humancomputerintegration/trigeminal-based-temperature-illusions/Schematic/Kicad/TrigTempIll_schematic.kicad_pcb

## EAGLE design schema/mjBeep/alimentazione.sch

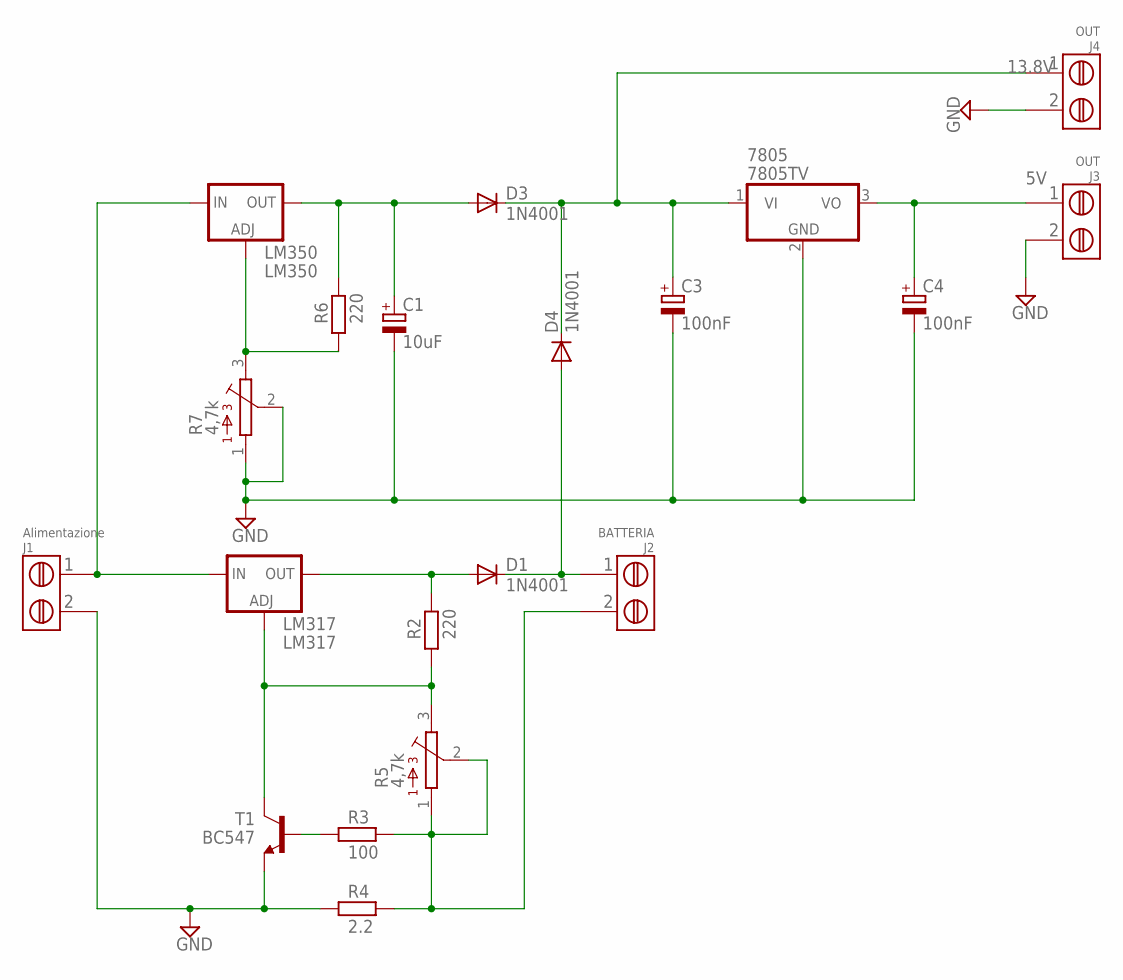
[picture p8: schematic alimentazione.sch]

Parts:
7805: 7805TV; TO220V
C1: 10uF; E2,5-6
C3, C4: 100nF; E2,5-6
D1, D3, D4: 1N4001; DO41-10
J1: Alimentazione; MORSETTIERA
J2: BATTERIA; MORSETTIERA
J3, J4: OUT; MORSETTIERA
LM317: LM317; 317TS
LM350: LM350; 317TS
R2, R6: 220; R1/4W
R3: 100; R1/4W
R4: 2.2; R1/4W
R5, R7: 4,7k; CA9V
T1: BC547; TO92

Connections:
5V: 7805.3 (VO), C4.+, J3.1
13.8V: 7805.1 (VI), C3.+, D3.C (K), D4.C (K), J4.1
+BAT: D1.C (K), D4.A, J2.1
-BAT: J2.2, R3.2, R4.2, R5.1, R5.2
GND: 7805.2 (GND), C1.-, C3.-, C4.-, J1.2, J3.2, J4.2, R4.1, R7.1, R7.2, T1.1 (E)
unnamed: C1.+, D3.A, LM350.2 (OUT), R6.2
unnamed: R3.1, T1.2 (B)
unnamed: LM350.1 (ADJ), R6.1, R7.3
unnamed: J1.1, LM317.3 (IN), LM350.3 (IN)
unnamed: D1.A, LM317.2 (OUT), R2.2
unnamed: LM317.1 (ADJ), R2.1, R5.3, T1.3 (C)
