humancomputerintegration/trigeminal-based-temperature-illusions/Schematic/Kicad/TrigTempIll_schematic.kicad_pcb

## EAGLE design schema/mjBeep/boardBase3.sch

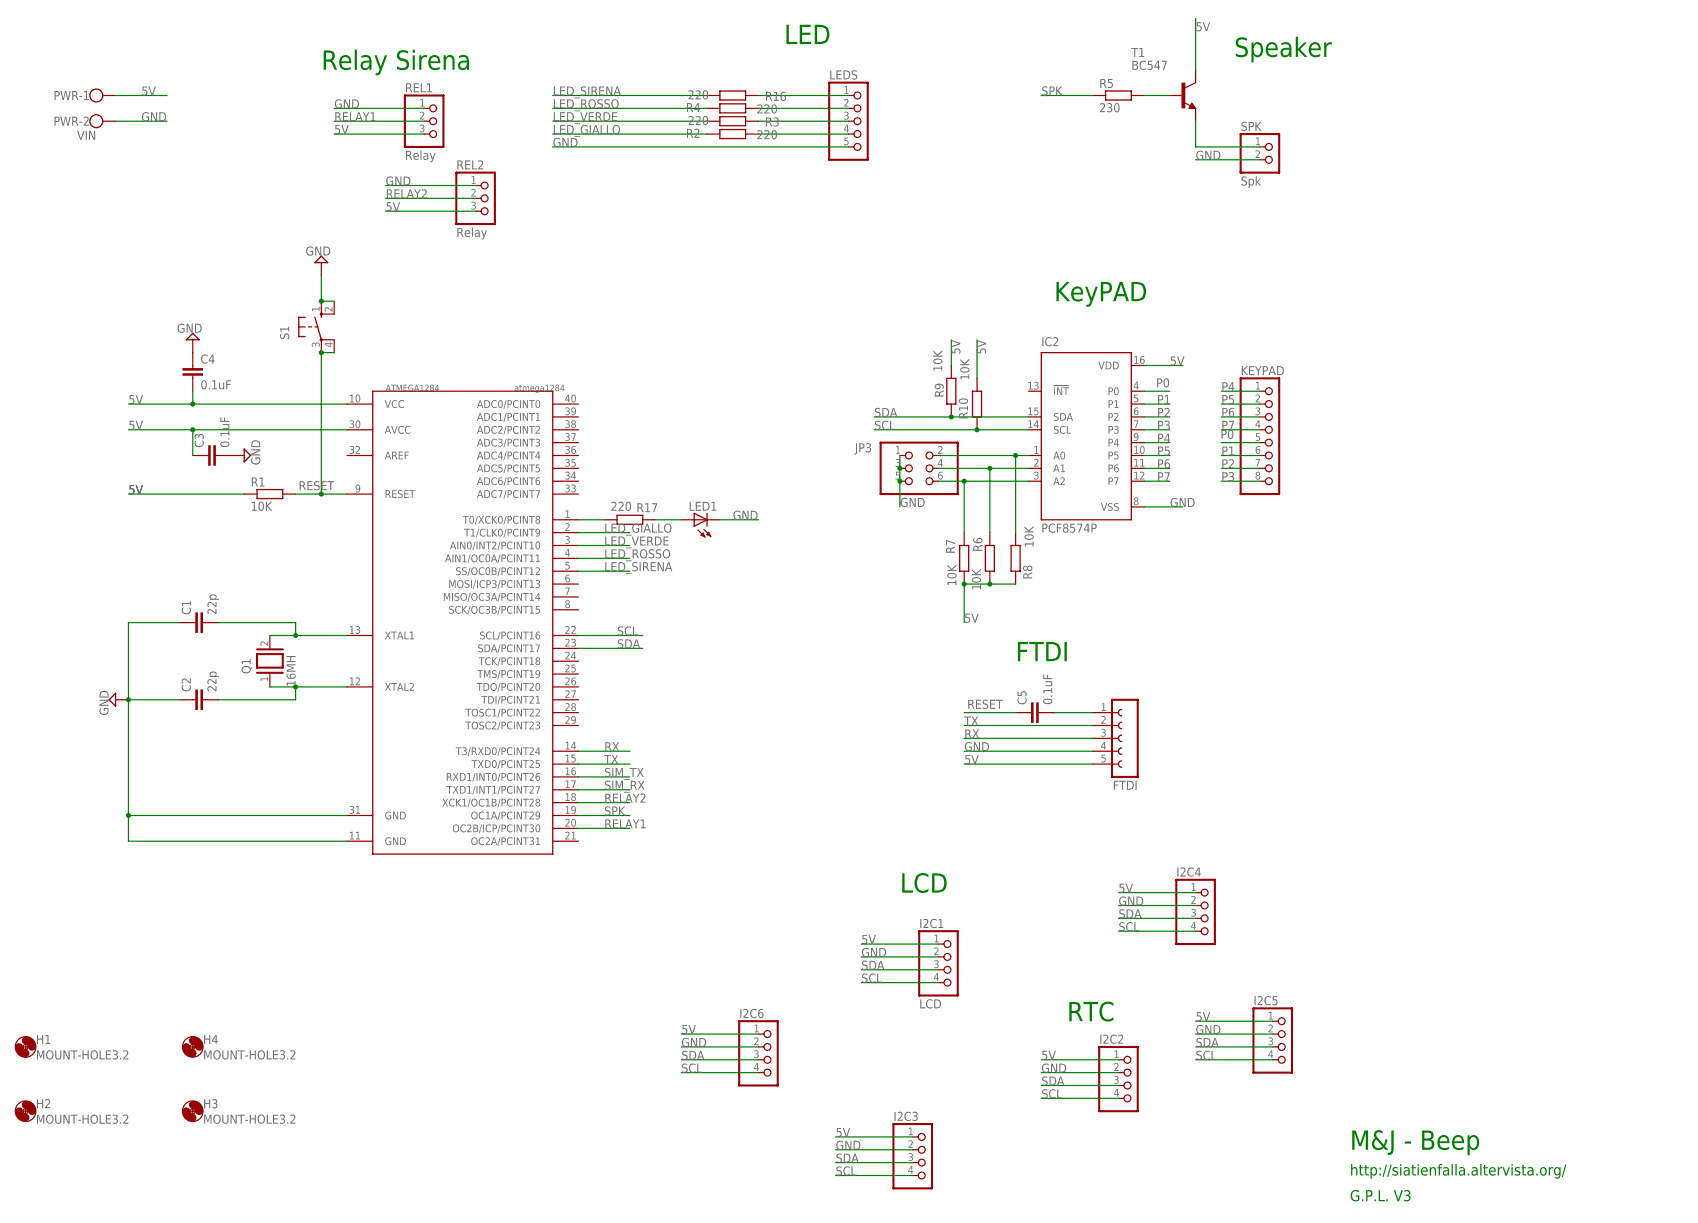
[picture p10: schematic boardBase3.sch]

Parts:
ATMEGA1284: atmega1284; DIL40
C1, C2: 22p; C025-024X044
C3, C4, C5: 0.1uF; C025-025X050
FTDI: FE05-1
H1, H2, H3, H4: MOUNT-HOLE3.2; 3,2
I2C1: LCD; 1X04
I2C2, I2C3, I2C4, I2C5, I2C6: PINHD-1X4; 1X04
IC2: PCF8574P; DIL16
JP3: PINHD-2X3; 2X03
KEYPAD: PINHD-1X8; 1X08
LED1: LED3MM
LEDS: PINHD-1X5; 1X05
PWR: VIN; W237-102
Q1: 16MH; QS
R1: 10K; 0207/10
R2, R3, R4, R16, R17: 220; 0207/2V
R5: 230; 0207/2V
R6, R7, R8, R9, R10: 10K; 0207/2V
REL1, REL2: Relay; 1X03
S1: 10-XX; B3F-10XX
SPK: Spk; 1X02
T1: BC547; TO92

Connections:
5V: ATMEGA1284.10 (VCC), ATMEGA1284.30 (AVCC), C3.1, C4.2, FTDI.5, I2C1.1, I2C2.1, I2C3.1, I2C4.1, I2C5.1, I2C6.1, IC2.16 (VDD), PWR.1, R1.1, R6.1, R7.2, R8.2, R9.2, R10.1, REL1.3, REL2.3, T1.3 (C)
GND: ATMEGA1284.11 (GND), ATMEGA1284.31 (GND), C1.1, C2.1, C3.2, C4.1, FTDI.4, I2C1.2, I2C2.2, I2C3.2, I2C4.2, I2C5.2, I2C6.2, IC2.8 (VSS), JP3.1, JP3.3, JP3.5, LED1.K (C), LEDS.5, PWR.2, REL1.1, REL2.1, S1.1 (S), S1.2 (S1), SPK.2
LED_GIALLO: ATMEGA1284.2 (T1/CLK0/PCINT9), R2.2
LED_ROSSO: ATMEGA1284.4 (AIN1/OC0A/PCINT11), R4.2
LED_SIRENA: ATMEGA1284.5 (SS/OC0B/PCINT12), R16.1
LED_VERDE: ATMEGA1284.3 (AIN0/INT2/PCINT10), R3.1
unnamed: ATMEGA1284.12 (XTAL2), C2.2, Q1.1
unnamed: ATMEGA1284.13 (XTAL1), C1.2, Q1.2
unnamed: IC2.1 (A0), JP3.2, R8.1
unnamed: C5.2, FTDI.1
unnamed: IC2.2 (A1), JP3.4, R6.2
unnamed: IC2.3 (A2), JP3.6, R7.1
unnamed: LEDS.4, R2.1
unnamed: LEDS.3, R3.2
unnamed: LEDS.2, R4.1
unnamed: R5.2, T1.2 (B)
unnamed: SPK.1, T1.1 (E)
unnamed: LEDS.1, R16.2
unnamed: ATMEGA1284.1 (T0/XCK0/PCINT8), R17.1
unnamed: LED1.A, R17.2
P0: IC2.4 (P0), KEYPAD.5
P1: IC2.5 (P1), KEYPAD.6
P2: IC2.6 (P2), KEYPAD.7
P3: IC2.7 (P3), KEYPAD.8
P4: IC2.9 (P4), KEYPAD.1
P5: IC2.10 (P5), KEYPAD.2
P6: IC2.11 (P6), KEYPAD.3
P7: IC2.12 (P7), KEYPAD.4
RELAY1: ATMEGA1284.20 (OC2B/ICP/PCINT30), REL1.2
RELAY2: ATMEGA1284.18 (XCK1/OC1B/PCINT28), REL2.2
RESET: ATMEGA1284.9 (RESET), C5.1, R1.2, S1.3, S1.4 (P1)
RX: ATMEGA1284.14 (T3/RXD0/PCINT24), FTDI.3
SCL: ATMEGA1284.22 (SCL/PCINT16), I2C1.4, I2C2.4, I2C3.4, I2C4.4, I2C5.4, I2C6.4, IC2.14 (SCL), R10.2
SDA: ATMEGA1284.23 (SDA/PCINT17), I2C1.3, I2C2.3, I2C3.3, I2C4.3, I2C5.3, I2C6.3, IC2.15 (SDA), R9.1
SIM_RX: ATMEGA1284.17 (TXD1/INT1/PCINT27)
SIM_TX: ATMEGA1284.16 (RXD1/INT0/PCINT26)
SPK: ATMEGA1284.19 (OC1A/PCINT29), R5.1
TX: ATMEGA1284.15 (TXD0/PCINT25), FTDI.2

Notes on the sheet:
Speaker
Relay Sirena
LED
M&J - Beep
http://siatienfalla.altervista.org/
G.P.L. V3
FTDI
KeyPAD
RTC
LCD
