humancomputerintegration/trigeminal-based-temperature-illusions/Schematic/Kicad/TrigTempIll_schematic.kicad_pcb

## EAGLE design schema/mjBeep/boardBase.sch

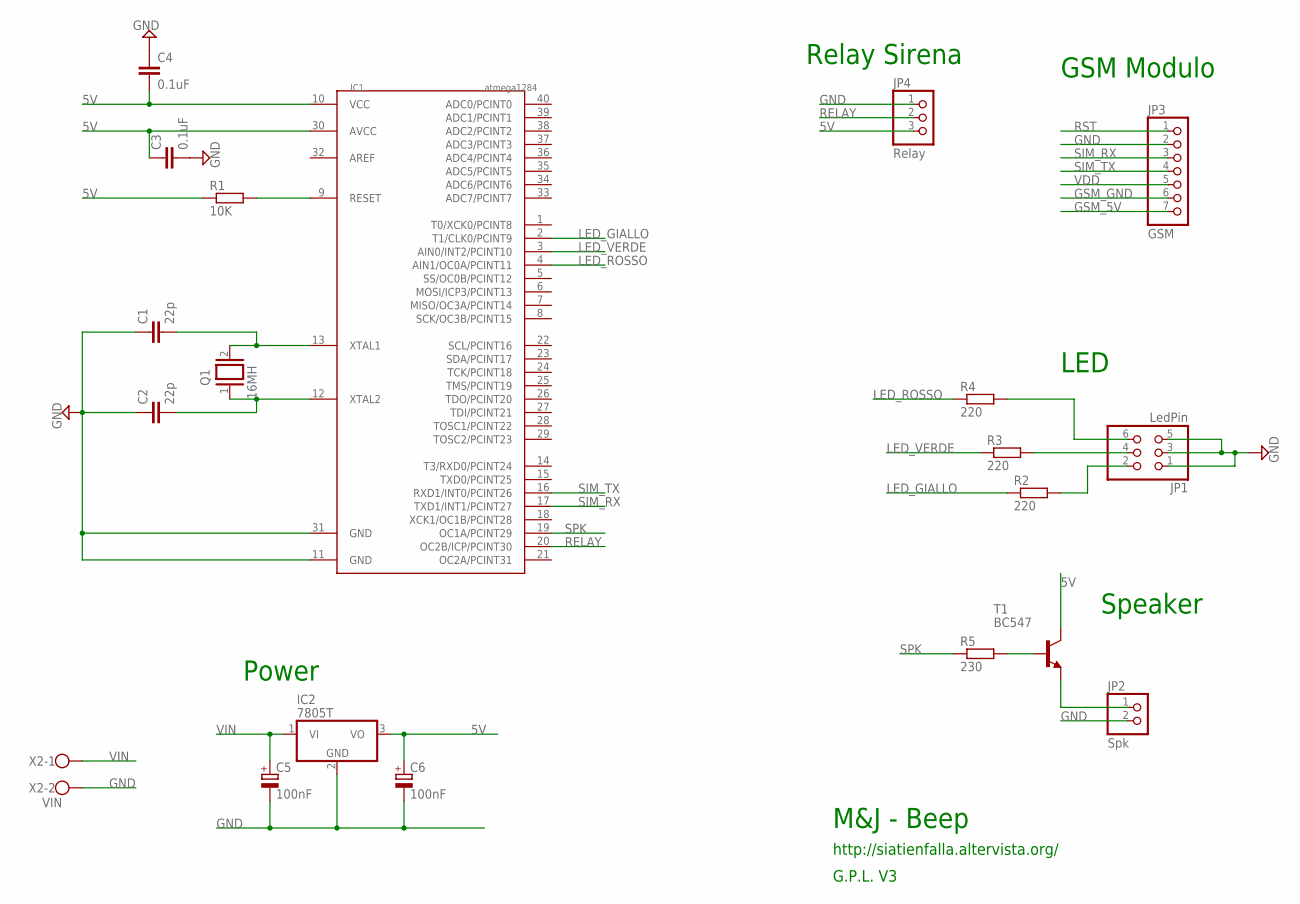
[picture p11: schematic boardBase.sch]

Parts:
C1, C2: 22p; C025-024X044
C3, C4: 0.1uF; C025-025X050
C5, C6: 100nF; E3,5-10
IC1: atmega1284; DIL40
IC2: 7805T; TO220H
JP1: LedPin; 2X03
JP2: Spk; 1X02
JP3: GSM; 1X07
JP4: Relay; 1X03
Q1: 16MH; QS
R1: 10K; 0207/10
R2, R3, R4: 220; 0207/10
R5: 230; 0207/10
T1: BC547; TO92
X2: VIN; W237-102

Connections:
5V: C3.1, C4.2, C6.+, IC1.10 (VCC), IC1.30 (AVCC), IC2.3 (VO), JP4.3, R1.1, T1.3 (C)
GND: C1.1, C2.1, C3.2, C4.1, C5.-, C6.-, IC1.11 (GND), IC1.31 (GND), IC2.2 (GND), JP1.1, JP1.3, JP1.5, JP2.2, JP3.2, JP4.1, X2.2
GSM_5V: JP3.7
GSM_GND: JP3.6
LED_GIALLO: IC1.2 (T1/CLK0/PCINT9), R2.1
LED_ROSSO: IC1.4 (AIN1/OC0A/PCINT11), R4.1
LED_VERDE: IC1.3 (AIN0/INT2/PCINT10), R3.1
unnamed: C2.2, IC1.12 (XTAL2), Q1.1
unnamed: C1.2, IC1.13 (XTAL1), Q1.2
unnamed: IC1.9 (RESET), R1.2
unnamed: JP1.2, R2.2
unnamed: JP1.4, R3.2
unnamed: JP1.6, R4.2
unnamed: R5.2, T1.2 (B)
unnamed: JP2.1, T1.1 (E)
RELAY: IC1.20 (OC2B/ICP/PCINT30), JP4.2
RST: JP3.1
SIM_RX: IC1.17 (TXD1/INT1/PCINT27), JP3.3
SIM_TX: IC1.16 (RXD1/INT0/PCINT26), JP3.4
SPK: IC1.19 (OC1A/PCINT29), R5.1
VDD: JP3.5
VIN: C5.+, IC2.1 (VI), X2.1

Notes on the sheet:
Speaker
Relay Sirena
LED
Power
GSM Modulo
M&J - Beep
http://siatienfalla.altervista.org/
G.P.L. V3
